tondy666/Vending-Machine-okeoce-V2/Inc/MyLCD.h

/*
 * MyLCD.h
 *
 *  Created on: Nov 21, 2019
 *      Author:
 */

#ifndef INC_MYLCD_H_
#define INC_MYLCD_H_


#define LCD_EN()			{ HAL_GPIO_WritePin(LCD_EN_GPIO_Port, LCD_EN_Pin, GPIO_PIN_SET);\
							  for(uint16_t i=0; i<1500; i++);;\
							  HAL_GPIO_WritePin(LCD_EN_GPIO_Port, LCD_EN_Pin, GPIO_PIN_RESET);\
							  for(uint16_t i=0; i<1500; i++);}

#define LCD_RW(state)		{HAL_GPIO_WritePin(LCD_RW_GPIO_Port, LCD_RW_Pin, (state)? GPIO_PIN_SET : GPIO_PIN_RESET);}
#define LCD_RS(state)		{HAL_GPIO_WritePin(LCD_RS_GPIO_Port, LCD_RS_Pin, (state)? GPIO_PIN_SET : GPIO_PIN_RESET);}
#define LCD_Command(data)	{LCD_Send(0,data);}
#define LCD_Data(data)		{LCD_Send(1,data);}

void LCD_Write4Bit(uint8_t);
void LCD_Send(_Bool, uint8_t);
void LCD_Init(void);
void LCD_Print(char *);
void LCD_PrintNum(uint16_t);
void LCD_SetCursor(uint8_t, uint8_t);
void LCD_Clear(void);


#endif /* INC_MYLCD_H_ */
