tondy666/Vending-Machine-okeoce-V2/Inc/MyUART.h

/*
 * MyUART.h
 *
 *  Created on: Nov 22, 2019
 *      Author:
 */

#ifndef INC_MYUART_H_
#define INC_MYUART_H_

#include "string.h"
#include "stdio.h"

void UART_Print(char *);
void UART_Println( char *);
void UART_PrintNum(uint16_t);



#endif /* INC_MYUART_H_ */
